qb-creates/lumi-square/eda/lumi-square/Capture.JPG

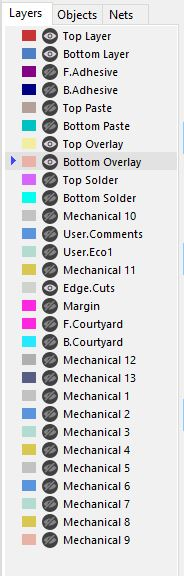
eda/lumi-square/Capture.JPG
