qb-creates/lumi-square/software/lumi-square-samd21/src/components/GameStates/LightDash/lightdashstate.h

#ifndef LIGHTDASH_H
#define LIGHTDASH_H

#include "timer.h"
#include "basestate.h"
#include "colors.h"
class LightDashState : public GameBaseState
{
public:
    LightDashState();
    void enterState(GameState previousState);
    void exitState();
    void updateState();
    void onButtonPressed(int8_t buttonIndex);

private:
    Timer timer;
    int8_t scoreDeductionAmount;
    int8_t bonusLedPointValue;
    int16_t maxLedTurnOffTime;
    int16_t minLedTurnOffTime;
    int16_t bonusLedTurnOffTime;
    bool enablePowerUps;
    bool bonusLedActive;
    Timer ledTurnOffTimers[16];
    void updateLedOffTimers();
    void updateGameTimer();
    void turnOnRandomLed();
    void turnOffSelectedLed(int8_t buttonIndex);
    void deductPointsFromScore();
    void addPointsToScore(int8_t buttonIndex);
    void playMusicNote(int8_t buttonIndex);
};

#endif
