qb-creates/lumi-square/software/lumi-square-samd21/src/components/Managers/statemanager.cpp

#include "statemanager.h"
#include "buttons.h"

StateManager::StateManager()
    : currentState(),
      powerOnState(),
      gameOverState(),
      mainMenuState(),
      memoryMatchingState(),
      lightSpeedState(),
      simonState(),
      stateDictionary{}
{
    stateDictionary[0] = &powerOnState;
    stateDictionary[1] = &gameOverState;
    stateDictionary[2] = &mainMenuState;
    stateDictionary[3] = &memoryMatchingState;
    stateDictionary[5] = &lightSpeedState;
    stateDictionary[6] = &simonState;
    currentState = &powerOnState;
    currentState->enterState(GameState::None);
}

StateManager &StateManager::Instance()
{
    static StateManager instance;
    return instance;
}

void StateManager::onFixedUpdate()
{
    buttonPressed();
    update();
}

void StateManager::update()
{
    currentState->updateState();
    GameState stateKey = currentState->switchStateCheck();

    if (stateKey != GameState::None)
    {
        GameBaseState *nextState = stateDictionary[static_cast<int8_t>(stateKey)];

        if (currentState != nextState)
        {
            GameState previousState = currentState->currentState;
            currentState->exitState();
            currentState = nextState;
            currentState->enterState(previousState);
        }
    }
}

void StateManager::buttonPressed()
{
    for (int i = 0; i < 16; i++)
    {
        if (Input::getButtonDown(i))
        {
            currentState->onButtonPressed(i);
        }
    }
}
