qb-creates/lumi-square/software/lumi-square-samd21/src/components/GameStates/MemoryMatching/matchingstate.h

#ifndef MATCHINGSTATE_H
#define MATCHINGSTATE_H

#include "../basestate.h"
#include "../../Colors/colors.h"
#include "timer.h"
class MemoryMatchingState : public GameBaseState
{
public:
    MemoryMatchingState();
    void enterState(GameState previousState);
    void exitState();
    void updateState();
    void onButtonPressed(int8_t buttonIndex);

private:
    Timer ledBrightnessAdjustTimer;
    int8_t correctMatches;
    int8_t selectedLedIndex1;
    int8_t selectedLedIndex2;
    bool isGuessCorrect;
    Color colorList[16];
    void shuffleLedColors();
    void evaluateGuess();
    void adjustLedBrightness();
};

#endif
