qb-creates/lumi-square/software/lumi-square-samd21/src/components/Managers/shutdownutility.h

#ifndef SLEEPMANAGER_H
#define SLEEPMANAGER_H

#include <stdint.h>

class ShutdownUtility
{
public:
    static ShutdownUtility& Instance();
    void setShutdownTimeout(uint32_t timeout);
    void resetShutdownTimer();
    void onFixedUpdate();

private:
    volatile uint32_t m_shutdownTimer;
    uint32_t m_shutdownTime;

private:
    ShutdownUtility();
    ShutdownUtility(const ShutdownUtility &) = delete;
    void operator=(const ShutdownUtility &) = delete;
    void updateShutdownTimer();
};

#endif
