qb-creates/lumi-square/software/lumi-square-samd21/src/components/Managers/gameproperties.h

#ifndef GAMEPROPERTIES_H
#define GAMEPROPERTIES_H

#include <stdint.h>

enum class GameState
{
    None = -1,
    PowerOn = 0,
    GameOver = 1,
    Menu = 2,
    MemoryMatching = 3,
    LightDash = 5,
    Simon = 6
};

enum class Difficulty
{
    Easy,
    Medium,
    Hard
};

class GameProperties
{
public:
    Difficulty gameDifficulty;
    static GameProperties &Instance();
    Difficulty increaseDifficulty();
    void setDifficulty(Difficulty difficulty);

private:
    GameProperties();
    GameProperties(const GameProperties &) = delete;
    void operator=(const GameProperties &) = delete;
    int8_t difficultyCount;
};
#endif
